phooky/Servitron/bone/src/motor.h

#ifndef MOTOR_H
#define MOTOR_H

#include "pwm.h"
#include <stdint.h>
#include <string>
class Motor {
private:
  PWM& pwm;
  
  uint8_t* gpioMap;
  int gpioFd;
public:
  Motor(PWM& pwm);

  bool init();
  void shutdown();

  // Set the motor to the specified
  // power. 0 is off. Negative values are CCW, positive
  // are CW.
  void setPower(int channel, int value = 0);
};

#endif // MOTOR_H
