phooky/Servitron/bone/config.h

#ifndef CONFIG_H
#define CONFIG_H

// All inputs are on port 2
#define Q0A 2
#define Q0B 3
#define Q0I 5

#define Q1A 4
#define Q1B 1
#define Q1I 25

#define Q2A 17
#define Q2B 16
#define Q2I 14

#define Q3A 15
#define Q3B 12
#define Q3I 13

#define Q4A 10
#define Q4B 11
#define Q4I 8

#define Q5A 9
#define Q5B 6
#define Q5I 7

// Brake is on port 0
#define BRAKE_PIN 26

#endif // CONFIG_H
