phooky/Servitron/bone/motor_test.cc

#include "motor.h"
#include <unistd.h>
#include <stdlib.h>
#include "brake.h"

void testMotor(int idx,Motors& m) {
  m.setPower(idx,0.33);
  sleep(1);
  m.setPower(idx,-0.33);
  sleep(1);
  m.setPower(idx,0);
}

int main(int argc, char** argv) {
  Brake b;
  b.setBrake(false);
  Motors m;
  m.enable(true);
  if (argc < 2) {
    testMotor(0,m);
  } else {
    for (int i = 1; i < argc; i++) {
      int idx = atoi(argv[i]);
      if (idx >= 0 && idx < 6) {
        testMotor(idx,m);
      }
    }
  }
  m.enable(false);
  b.setBrake(true);
}
